jclements3/clements49/openscad/parts/sb_harp_wood_inside1.scad

// SOUNDBOX part: harp_wood_inside1
// Inner lining strip. Thin in the e2 direction (OBB thickness ~2.98 model units),
// broad face spans e0 (sweep/stacking axis, ~17.72) x e1 (~7.10).
// Cross-section outline shape varies along the e0 axis -> built as a LOFT:
// hull() of consecutive stacked cross-section polygons (each linear_extrude'd a hair).
//
// Frame contract: rebuild in part PRINCIPAL frame, place with multmatrix.
//   world = centroid + u*e1 + v*e2 + w*e0   (local x=u along e1, y=v along e2, z=w along e0)
// Outline points are (e1, e2) pairs; sections are positioned at z = s along e0.

module sb_harp_wood_inside1() {
    // ---- key dimensions (model world units) ----
    // OBB extents: e0=17.717 (sweep), e1=7.103 (width), e2=2.977 (thickness, thin axis)
    eps = 0.001;            // slab thickness used per section for hull lofting

    // centroid (world)
    cx = -4.670895242189419;
    cy = -32.86783006658697;
    cz = 179.47082189015964;

    // principal axes
    // e0 (section/stacking axis), e1 (outline x), e2 (outline y, thin)
    e0 = [-7.198236352063046e-08, 0.5435756491694905, 0.8393601811081832];
    e1 = [-3.8562726048548236e-05, 0.839360180482577, -0.5435756487676503];
    e2 = [0.9999999992564554, 3.2407144580085266e-05, -2.090133971594858e-05];

    // section positions along e0 (local z) and their (e1,e2) outlines
    s = [
        -5.445743567141493,
        -2.4929627001441386,
        0.45981816685321597,
        3.4125990338505705,
        6.365379900847925,
        9.31816076784528,
        12.270941634842634
    ];

    outline0 = [
        [-0.28423858061108387, 1.488589415933371],
        [-0.28412097685894766, -1.4886113282819196],
        [-0.037238011977131835, -1.4886018432883672],
        [0.46663292684326274, -1.4885824645214034],
        [0.5771064702357185, -1.4870652117922991],
        [0.6285866266420308, -1.485607450292956],
        [0.6877653271956894, -1.470423157369534],
        [0.7000740725017132, -1.3924884191281677],
        [0.7026030400469345, -0.9560731261482711],
        [0.7025378561735616, 0.9561275620747436],
        [0.6999753492587257, 1.3925428977992214],
        [0.6876523202368277, 1.4704769278158705],
        [0.6284641586642077, 1.4856552405996881],
        [0.5769838903505793, 1.48710976204192],
        [0.46651343259493316, 1.4886182796209617],
        [0.16757433444905967, 1.4886072631346956]
    ];

    outline1 = [
        [-2.2211947008880837, 1.4885149353038583],
        [-2.2210802990409326, -1.488685809034434],
        [-1.1255523244791623, -1.488643703018274],
        [-0.5278931458392201, -1.488620724589759],
        [-0.037238011977131835, -1.4886018432883672],
        [0.04289933822961878, -1.4870857601435665],
        [0.08902997589549422, -1.4764972492085515],
        [0.10672122392953276, -1.3932961147342884],
        [0.1092447784548436, -0.9560959480282831],
        [0.10920803936049572, 4.515133049092299e-06],
        [0.10917130027530653, 0.9561047398758028],
        [0.10662244039492941, 1.3933042348610105],
        [0.0889247982433845, 1.476504009687727],
        [0.04279334694764336, 1.48708945274709],
        [-0.03735241382428245, 1.4885989010499256],
        [-0.4884652114010084, 1.4885817935922496],
        [-1.1256501377231491, 1.488557280376455]
    ];

    outline2 = [
        [-3.7660075997312097, 1.4884555318457646],
        [-3.765893197884059, -1.4887452124925282],
        [-0.5213326521875876, -1.4886205396602965],
        [-0.011937596648640247, -1.4870879643085595],
        [0.09594495176406193, -1.4764970804691762],
        [0.11385308403864391, -1.3932959374691758],
        [0.11639978513572624, -0.9560957698465659],
        [0.11632630695618618, 0.9561049180575201],
        [0.11373931284420502, 1.3933044115497653],
        [0.0958199835946415, 1.4765041776662424],
        [-0.012051882236779665, 1.4870872482631672],
        [-0.5214387597285743, 1.488580204996925],
        [-1.553588078503163, 1.488540805686649]
    ];

    outline3 = [
        [-4.723523455708495, 1.4884187070218255],
        [-4.723409053861344, -1.4887820373164673],
        [-4.707726671315054, -1.4887814586841805],
        [-0.28671187640929485, -1.488611543641521],
        [-0.003589048072957457, -1.4885997406002451],
        [0.8983161288740833, -1.4870535031523562],
        [1.6675546817343883, -1.4754005782067228],
        [1.6674313941580925, 1.4755281072835964],
        [0.898213339478771, 1.48712218669846],
        [-0.0037034498651404846, 1.4885995732265742],
        [-1.804047564743576, 1.4885309092462617],
        [-4.308168738395276, 1.4884346832777189]
    ];

    outline4 = [
        [-4.707837871248055, 1.4884190473585353],
        [-4.707726671315054, -1.4887814586841805],
        [-3.8931636419651827, -1.4887501986067415],
        [-1.2486494798911787, -1.488648576857551],
        [-0.003589048072957457, -1.4885997406002451],
        [1.0916765075924113, -1.4870456296219972],
        [1.5817564910248378, -1.4855700459115404],
        [2.1223212090011883, -1.4753816883836677],
        [2.347302295768502, -1.393013734405529],
        [2.3796327019090335, -0.9560084031372116],
        [2.3796042571758145, 9.062983157617328e-05],
        [2.379559223747816, 0.9561918079297159],
        [2.3471952329983496, 1.3931944163085073],
        [2.122207816738517, 1.475545566975609],
        [1.5816423173806624, 1.4856919300442955],
        [1.0915622219951109, 1.4871298213683084],
        [-0.0037034498651404846, 1.4885995732265742],
        [-1.2487638817383293, 1.488552167480741],
        [-2.9212122155895672, 1.4884879307064505]
    ];

    outline5 = [
        [-2.665845037069713, 1.488497671003108],
        [-2.6657306352225625, -1.488703073335185],
        [0.011619597568966356, -1.4870871675198238],
        [0.8084718621407894, -1.476468868390543],
        [1.1252608702512332, -1.3932571993227907],
        [1.170493946504207, -0.9560553921558652],
        [1.1704655017343435, 4.4594487238224526e-05],
        [1.1704204683429902, 0.9561448189110628],
        [1.1251537924104658, 1.393343149953579],
        [0.8083666845161694, 1.4765316752499993],
        [0.011513606277830046, 1.4870882837894122]
    ];

    outline6 = [
        [-1.3929881582241253, 1.487034028716704],
        [-1.3928738726176633, -1.4871416606921806],
        [-0.4396003210213495, -1.476517350421667],
        [-0.04585224169721336, -1.3933022468277474],
        [0.010381785559919088, -0.9561000168725035],
        [0.010351739837562768, -3.029090070105441e-08],
        [0.010308307389539806, 0.9561004326130031],
        [-0.045949424288484586, 1.3932983412476305],
        [-0.43971379295213353, 1.4764831928999458]
    ];

    outlines = [outline0, outline1, outline2, outline3, outline4, outline5, outline6];

    // place in world via principal frame:
    // local x -> e1, local y -> e2, local z -> e0
    multmatrix([
        [e1[0], e2[0], e0[0], cx],
        [e1[1], e2[1], e0[1], cy],
        [e1[2], e2[2], e0[2], cz],
        [0,     0,     0,     1 ]
    ]) {
        // loft: hull consecutive thin slabs placed at z = s[i] along e0
        for (i = [0 : len(s) - 2]) {
            hull() {
                translate([0, 0, s[i]])
                    linear_extrude(height = eps)
                        polygon(points = outlines[i]);
                translate([0, 0, s[i + 1]])
                    linear_extrude(height = eps)
                        polygon(points = outlines[i + 1]);
            }
        }
    }
}

sb_harp_wood_inside1();
