jclements3/clements49/cad/scaffold/harp_scaffold.scad

// ============================================================
// harp_scaffold.scad  —  Clements 49 frame (REAL model) + 49 strings
// Real components imported from parts/ (mesh from the TurboSquid OBJ,
// millimetres, world frame, 75.5 in / 1918 mm tall).
// The SOUNDBOX is the limacon generator from soundbox_limacon.scad (the §11
// handoff), integrated here. Default = clean OUTER body (verified manifold);
// hollow graded-wall version is gated off (known-broken cavity cut — see that file).
// strings: 49 = original 47 + 2 added in the BASS. [board_xyz, pin_xyz] mm.
// ============================================================
use <soundbox_limacon.scad>;   // provides module soundbox_limacon(hollow=false)
$fn = 28;
string_dia = 2.0;   // mm, visual

module pillar() color([0.55,0.35,0.20]) import("parts/pillar.stl");
module neck()   color([0.90,0.80,0.50]) import("parts/neck.stl");
module base()   color([0.50,0.50,0.55]) import("parts/base.stl");

strings_49 = [
  [[-297.4,-2.7,111.8],[-315.8,14.9,1833.5]],
  [[-279.2,-2.7,141.5],[-296.7,14.9,1833.5]],
  [[-260.9,-2.8,171.2],[-277.6,14.9,1833.5]],
  [[-242.7,-2.8,200.9],[-258.5,14.9,1833.5]],
  [[-226.4,-2.1,227.5],[-242.0,15.6,1833.1]],
  [[-208.6,-2.1,256.5],[-223.7,15.6,1832.8]],
  [[-191.3,-2.1,284.7],[-203.8,15.6,1830.5]],
  [[-174.1,-2.1,312.8],[-186.2,15.6,1826.2]],
  [[-155.3,-2.2,343.4],[-167.0,15.6,1821.4]],
  [[-137.0,-2.2,373.3],[-148.2,15.6,1815.3]],
  [[-120.5,-2.2,400.2],[-131.3,15.6,1807.2]],
  [[-102.9,-2.2,428.9],[-113.3,15.6,1797.4]],
  [[-87.7,-2.2,453.6],[-97.7,15.6,1787.2]],
  [[-72.3,-2.2,478.7],[-81.9,15.6,1775.3]],
  [[-55.0,-2.2,507.0],[-64.2,15.6,1759.3]],
  [[-40.3,-2.3,530.8],[-49.2,15.6,1743.4]],
  [[-22.2,-2.3,560.4],[-30.6,15.6,1721.7]],
  [[-4.9,-2.3,588.5],[-12.9,15.6,1695.8]],
  [[15.9,-2.3,622.5],[8.5,15.6,1658.8]],
  [[36.3,-2.3,655.7],[29.3,15.6,1620.7]],
  [[53.7,-2.3,684.0],[47.1,15.6,1580.6]],
  [[70.1,-2.4,710.8],[64.0,15.6,1541.6]],
  [[86.3,-2.4,737.2],[80.5,15.6,1504.7]],
  [[100.3,-2.4,759.9],[94.9,15.6,1469.1]],
  [[114.1,-2.4,782.5],[109.0,15.6,1437.6]],
  [[126.0,-2.4,801.8],[121.2,15.6,1413.9]],
  [[138.6,-2.4,822.3],[134.1,15.6,1391.6]],
  [[152.9,-2.4,845.7],[148.8,15.6,1373.5]],
  [[167.5,-2.4,869.5],[163.7,15.6,1360.0]],
  [[180.9,-2.5,891.3],[177.4,15.6,1352.4]],
  [[196.3,-2.5,916.3],[193.2,15.6,1348.5]],
  [[210.3,-2.5,939.3],[207.6,15.6,1345.9]],
  [[224.5,-2.5,962.3],[222.0,15.6,1345.3]],
  [[237.9,-2.5,984.2],[235.8,15.6,1347.6]],
  [[252.3,-2.5,1007.7],[250.6,15.6,1350.4]],
  [[268.2,-2.5,1033.6],[266.8,15.6,1355.9]],
  [[282.1,-2.5,1056.2],[281.0,15.6,1362.7]],
  [[294.9,-2.6,1077.1],[294.2,15.6,1370.3]],
  [[307.1,-2.6,1097.1],[306.7,15.6,1379.9]],
  [[318.3,-2.6,1115.3],[318.2,15.6,1386.5]],
  [[330.0,-2.6,1134.4],[330.2,15.6,1395.3]],
  [[341.1,-2.6,1152.5],[341.5,15.6,1404.7]],
  [[353.5,-2.6,1172.7],[354.2,15.6,1415.3]],
  [[365.3,-2.6,1192.0],[366.3,15.6,1425.4]],
  [[376.2,-2.6,1209.8],[377.5,15.6,1433.8]],
  [[385.2,-2.6,1224.4],[386.7,15.6,1441.1]],
  [[394.7,-2.6,1240.0],[396.5,15.6,1448.4]],
  [[405.6,-3.2,1257.6],[407.5,15.6,1454.4]],
  [[417.2,-5.7,1262.8],[419.0,15.6,1459.2]]
];
module strings() color([0.20,0.40,0.90])
  for (s = strings_49) hull() {
    translate(s[0]) sphere(string_dia/2);
    translate(s[1]) sphere(string_dia/2);
  }

// Soundboard string-line interface (board ends), bass corner -> treble:
soundboard_bass_mm   = strings_49[0][0];
soundboard_treble_mm = strings_49[48][0];

// Soundbox = the limacon generator (use<soundbox_limacon.scad> above).
//   soundbox_limacon();            -> clean outer body (default, verified)
//   soundbox_limacon(hollow=true); -> graded-wall version (currently fragments)

// ---- assembly ----
pillar();
neck();
base();
strings();
color([0.80,0.55,0.30]) soundbox_limacon();
